xesscorp/XuLA2/FPGA/blinker/blinker.ucf

net clk_i     loc=a9;  # 12 MHz input clock.
net blinker_o loc=t7 | IOSTANDARD=LVTTL | DRIVE=24 | SLEW=SLOW ;  # Blinker output to LED.
